g2maurer/Retro_Clock/src/PMclockMenu.h

//
//  Definitions for Touch processing states
//
//
enum  menu { MAIN_MENU, WIFI_MENU, 
            ALARM_MENU, SSID_MENU, 
            PW_MENU, TZ_MENU,
            REGION_MENU, CITY_MENU,
};

#define NUMBER_KEYPAD 0x20
#define UC_KEYPAD 0x40
#define LC_KEYPAD 0x60

//#define PUSH_POP_DEBUG
